oddlama/opkey/contplot.py

#!/usr/bin/env python3

import glob
import math
import numpy as np
import pandas as pd
import plotly
import plotly.graph_objects as go
import os
import sys
import scipy
import scipy.io.wavfile
from scipy import signal

triggerVelocityThreshold = 1.0
maxTriggerDelayUs = 40000
minTriggerJitterDelayUs = 15000
releasePositionThreshold = 0.4
releasePositionAbsolute = 0.15
pedalReleaseThreshold = 0.1
pedalPressThreshold = 0.2
velocityEmaAlpha = 0.1

def IsValidVelocityMaximum(pos, vel):
    return (vel >= 10.0) or ((pos > .25) and (vel > 3.0))

class LogicState:
    def __init__(self):
        self.lastUpdateTime = 0
        self.pos = 0.0
        self.vel = 0.0
        self.velEma = 0.0

        self.changed = False
        self.pressed = False

        self.lastPressTime = 0
        self.pressVelocity = 0.0
        self.lastReleaseTime = 0

        self.maxVelTime = 0
        self.maxVel = 0.0
        self.maxVelEma = 0.0
        self.maxVelPos = 0.0

    def nextState(self, now, deltaTime, newData):
        velEmaAlpha = 0.1

        prevPos = self.pos
        prevVel = self.vel
        self.pos = newData
        self.vel = (self.pos - prevPos) * (1000000.0 / deltaTime)
        self.velEma = self.velEma * (1.0 - velEmaAlpha) + self.vel * velEmaAlpha

        self.changed = False
        if self.pressed:
            if (self.pos < releasePositionAbsolute) or ((self.maxVelPos - self.pos) > releasePositionThreshold * self.maxVelPos):
                self.pressed = False
                self.changed = True
                self.lastReleaseTime = now

                self.maxVelTime = 0
                self.maxVel = 0.0
                self.maxVelEma = 0.0
                self.maxVelPos = 0.0
        else:
            if self.vel > self.maxVel:
                if IsValidVelocityMaximum(self.pos, self.vel):
                    self.maxVelTime = now
                    self.maxVel = self.vel
                    self.maxVelEma = self.velEma
                    self.maxVelPos = self.pos

            if (prevVel > triggerVelocityThreshold) and (self.vel <= triggerVelocityThreshold):
                if ((now - self.maxVelTime) <= maxTriggerDelayUs) and (now - self.lastReleaseTime > minTriggerJitterDelayUs):
                    self.pressed = True
                    self.changed = True
                    self.lastPressTime = self.maxVelTime

                    linearMaxVelocity = 50.0
                    linearRange = 0.75
                    compressedMaxVelocity = 110.0

                    self.pressVelocity = self.maxVel - self.maxVelEma
                    if self.pressVelocity < 0.0:
                        self.pressVelocity = 0.0
                    elif self.pressVelocity < linearMaxVelocity:
                        self.pressVelocity = linearRange * self.pressVelocity / linearMaxVelocity
                    elif self.pressVelocity < compressedMaxVelocity:
                        self.pressVelocity = linearRange + (1.0 - linearRange) * (self.pressVelocity - linearMaxVelocity) / (compressedMaxVelocity - linearMaxVelocity)
                    else:
                        self.pressVelocity = 1.0
                else:
                    self.maxVelTime = 0
                    self.maxVel = 0.0
                    self.maxVelEma = 0.0
                    self.maxVelPos = 0.0

# Config
includeRaw=True

# Constants (DONT CHANGE!)
plotAxisPos = "y"
plotAxisPosRaw = "y3"
plotAxisVel = "y2"
plotAxisVelRaw = "y4"
plotAxisWav = "y5"
plotAxisTriggers = plotAxisPosRaw

maxKeyFreqDeviation = 0.05
keyFrequencies = {
    'A0'    : 27.50000, 'A+0'   : 29.13524, 'B0'    : 30.86771, 'C1'    : 32.70320,
    'C+1'   : 34.64783, 'D1'    : 36.70810, 'D+1'   : 38.89087, 'E1'    : 41.20344,
    'F1'    : 43.65353, 'F+1'   : 46.24930, 'G1'    : 48.99943, 'G+1'   : 51.91309,
    'A1'    : 55.00000, 'A+1'   : 58.27047, 'B1'    : 61.73541, 'C2'    : 65.40639,
    'C+2'   : 69.29566, 'D2'    : 73.41619, 'D+2'   : 77.78175, 'E2'    : 82.40689,
    'F2'    : 87.30706, 'F+2'   : 92.49861, 'G2'    : 97.99886, 'G+2'   : 103.8262,
    'A2'    : 110.0000, 'A+2'   : 116.5409, 'B2'    : 123.4708, 'C3'    : 130.8128,
    'C+3'   : 138.5913, 'D3'    : 146.8324, 'D+3'   : 155.5635, 'E3'    : 164.8138,
    'F3'    : 174.6141, 'F+3'   : 184.9972, 'G3'    : 195.9977, 'G+3'   : 207.6523,
    'A3'    : 220.0000, 'A+3'   : 233.0819, 'B3'    : 246.9417, 'C4'    : 261.6256,
    'C+4'   : 277.1826, 'D4'    : 293.6648, 'D+4'   : 311.1270, 'E4'    : 329.6276,
    'F4'    : 349.2282, 'F+4'   : 369.9944, 'G4'    : 391.9954, 'G+4'   : 415.3047,
    'A4'    : 440.0000, 'A+4'   : 466.1638, 'B4'    : 493.8833, 'C5'    : 523.2511,
    'C+5'   : 554.3653, 'D5'    : 587.3295, 'D+5'   : 622.2540, 'E5'    : 659.2551,
    'F5'    : 698.4565, 'F+5'   : 739.9888, 'G5'    : 783.9909, 'G+5'   : 830.6094,
    'A5'    : 880.0000, 'A+5'   : 932.3275, 'B5'    : 987.7666, 'C6'    : 1046.502,
    'C+6'   : 1108.731, 'D6'    : 1174.659, 'D+6'   : 1244.508, 'E6'    : 1318.510,
    'F6'    : 1396.913, 'F+6'   : 1479.978, 'G6'    : 1567.982, 'G+6'   : 1661.219,
    'A6'    : 1760.000, 'A+6'   : 1864.655, 'B6'    : 1975.533, 'C7'    : 2093.005,
    'C+7'   : 2217.461, 'D7'    : 2349.318, 'D+7'   : 2489.016, 'E7'    : 2637.020,
    'F7'    : 2793.826, 'F+7'   : 2959.955, 'G7'    : 3135.963, 'G+7'   : 3322.438,
    'A7'    : 3520.000, 'A+7'   : 3729.310, 'B7'    : 3951.066, 'C8'    : 4186.009,
    'Soft'  : 0.0,
    'Damp'  : 0.0,
}

def butter_bandpass(lowcut, highcut, fs, order=5):
    nyq = 0.5 * fs
    low = lowcut / nyq
    high = highcut / nyq
    b, a = signal.butter(order, [low, high], btype='band')
    return b, a

def butter_bandpass_filter(data, lowcut, highcut, fs, order=5):
    b, a = butter_bandpass(lowcut, highcut, fs, order=order)
    y = signal.lfilter(b, a, data)
    return y

def running_mean(x, N):
    cumsum = np.cumsum(np.insert(x, 0, 0))
    return (cumsum[N:] - cumsum[:-N]) / float(N)


#def butter_lowpass(cutoff, fs, order):
#    nyq = 0.5 * fs
#    normal_cutoff = cutoff / nyq
#    b, a = signal.butter(order, normal_cutoff, btype='low', analog=False)
#    return b, a
#
#def butter_lowpass_filter(data, cutoff, fs, order=5):
#    b, a = butter_lowpass(cutoff, fs, order=order)
#    y = signal.lfilter(b, a, data)
#    return y
#
#cutoff=50
#fs=1000000/(csv['time'].iloc[-1]/len(csv['time']))

def getInputFiles(inputPath):
    if os.path.isdir(inputPath):
        path = inputPath
        fileBasenames = glob.glob(os.path.join(path, "*.raw"))
        fileBasenames = [os.path.basename(f) for f in fileBasenames if os.path.isfile(f)]
        fileBasenames.sort(key=lambda f: os.path.getmtime(os.path.join(path, f)))
    elif os.path.isfile(inputPath):
        path = os.path.dirname(inputPath)
        fileBasenames = [os.path.basename(inputPath)]
    else:
        print("error: Given path is neither a directory nor a .raw file'".format(path))
        sys.exit(1)

    return (path, fileBasenames)

def setFigureLayout(fig):
    fig.update_traces(mode='lines')
    fig.update_layout(
        xaxis=dict(
            title="Time (ms)",
            domain=[.04,.92] if includeRaw else [0.0, 1.0],
            ),
        yaxis=dict(
            title="Position",
            overlaying="y",
            anchor="x",
            side="left",
            ),
        yaxis2=dict(
            title="Velocity",
            overlaying="y",
            anchor="x",
            side="right",
            ),
        yaxis5=dict(
            title="dB",
            overlaying="y",
            anchor="free",
            side="right",
            position=1.0,
            ),
        )
    if includeRaw:
        fig.update_layout(
            yaxis3=dict(
                title="Raw Position",
                overlaying="y",
                anchor="free",
                side="left",
                position=0.0,
                ),
            yaxis4=dict(
                title="Raw Velocity",
                overlaying="y",
                anchor="free",
                side="right",
                position=0.96,
                ),
            )
    fig.update_layout(
        template='plotly_dark',
        title="Sensor Plot"
        )

class Meta:
    def __init__(self, file):
        try:
            with open(file, 'r') as f:
                content = f.readlines()
            content = [l.strip() for l in content]
        except IOError:
            raise IOError("Could not open meta file '{}'".format(file))

        if len(content) != 5:
            raise IOError("Invalid meta content length")

        self.uniqueSessionId = int(content[0])
        self.hostOverallBegin = int(content[1])
        self.hostBegin = int(content[2])
        self.hostEnd = int(content[3])
        self.mcuElapsed = int(content[4])

    def getUniqueSessionId(self):
        return self.uniqueSessionId

    def getOverallBeginUsHost(self):
        return self.hostOverallBegin

    def getBeginUsHost(self):
        return self.hostBegin

    def getEndUsHost(self):
        return self.hostEnd

    def getElapsedUsHost(self):
        return self.hostEnd - self.hostBegin

    def getElapsedUsMcu(self):
        return self.mcuElapsed

    def getOverallOffsetSec(self):
        return (self.hostBegin - self.hostOverallBegin) / 1000000

class Capture:
    def __init__(self):
        pass

    @classmethod
    def fromFile(cls, path, basename):
        c = cls()
        c.path = path
        c.basename = basename
        c.name = os.path.splitext(basename)[0]
        c.meta = Meta(c.__getMetaFile())

        tokens = c.name.split('_')
        c.sensorName = tokens[1]
        c.num = tokens[2]
        c.identifier = "{}, #{}".format(c.sensorName, c.num)

        c.__readData()
        return c

    @classmethod
    def fromCaptures(cls, captures):
        c = cls()
        c.path = captures[0].path
        c.basename = captures[0].basename
        c.name = captures[0].name
        #c.meta = Meta(c.__getMetaFile())

        c.sensorName = captures[0].sensorName
        c.num = captures[-1].num
        c.identifier = "{}".format(c.sensorName)

        c.count = 0
        c.t = []
        c.tTriggers = []
        c.yTriggers = []
        c.rawPos = []
        c.rawVel = []
        c.wavT = []
        c.wavY = []
        for capture in captures:
            c.count += capture.count
            c.t.extend(capture.t)
            c.tTriggers.extend(capture.tTriggers)
            c.yTriggers.extend(capture.yTriggers)
            c.rawPos.extend(capture.rawPos)
            c.rawVel.extend(capture.rawVel)
            c.wavT.extend(capture.wavT)
            c.wavY.extend(capture.wavY)
        return c

    def __getRawFile(self):
        return os.path.join(self.path, self.basename)

    def __getMetaFile(self):
        return "{}.meta".format(self.__getRawFile())

    def getPlotHtmlFile(self):
        return "{}.html".format(os.path.join(self.path, self.name))

    def getWavFile(self):
        return os.path.join(self.path, "{}.wav".format(self.meta.uniqueSessionId))

    def getIdentifier(self):
        return self.identifier

    def __readData(self):
        # Read data
        self.csv = pd.read_csv(self.__getRawFile(), names=['time', 'dt', 'value'])

        self.rawTime = self.csv['time'].values
        self.rawDt = self.csv['dt'].values
        self.rawSensorData = self.csv['value'].values

        self.tTriggers = []
        self.yTriggers = []
        logicState = LogicState()
        for i in range(len(self.rawDt)):
            logicState.nextState(self.rawTime[i], self.rawDt[i], self.rawSensorData[i])
            if logicState.changed:
                if logicState.pressed:
                    self.tTriggers += [self.rawTime[i]]
                    self.yTriggers += [1]
                else:
                    self.tTriggers += [self.rawTime[i]]
                    self.yTriggers += [0]

        # General information
        self.count = len(self.rawSensorData)
        #self.tStep = (self.meta.getElapsedNsMcu() / 1000000000) / self.count
        #if self.tStep < 4000:
        #    frac = int(0.004 / self.tStep)
        #    self.tStep *= frac
        #    self.rawSensorData = [self.rawSensorData[i] for i in range(0, self.count, frac)]
        #    self.count = len(self.rawSensorData)

        #self.tStepInv = self.count / (self.meta.getElapsedNsMcu() / 1000000000)

        #self.t0 = self.rawTime[0]
        #self.t = [(x - self.t0) / 1000 for x in self.csv['time'].values]
        self.t = [self.meta.getOverallOffsetSec() + i / 1000000 for i in self.rawTime]
        self.rawPos = self.rawSensorData
        self.rawVel = [0] + [(self.rawPos[i + 1] - self.rawPos[i]) * (1000000.0 / self.rawDt[i + 1]) for i in range(len(self.rawPos) - 1)]

        ### Calculate pos and vel
        ##self.rawPos = self.rawSensorData
        ##self.rawVel = np.insert(np.diff(self.rawPos) * self.tStepInv, 0, 0)
        ##global aat
        ##aat = .0
        ##def accumTen(i):
        ##    global aat
        ##    aat = aat * .9 + i * .1
        ##    return aat
        ##self.emaPos = [accumTen(i) for i in self.rawPos]
        ##global bbt
        ##bbt = .0
        ##def accumTen2(i):
        ##    global bbt
        ##    if i < bbt:
        ##        bbt = bbt * .7 + i * .3
        ##    else:
        ##        bbt = bbt * .9 + i * .1
        ##    return bbt
        ##self.emaVel = [accumTen2(i) for i in self.rawVel]
        ###self.smoothPos = signal.savgol_filter(self.rawPos, 153, 3)
        ###self.smoothVel = signal.savgol_filter(self.rawVel, 153, 3)

        ### Calculate time shift
        ##self.indexT0 = np.where(self.rawVel == np.amax(self.rawVel))[0][0]
        ##self.t0 = -self.csv['time'].values[self.indexT0]
        ##self.t = [(self.t0 + x) / 1000 for x in self.csv['time'].values]

        ### Calculate t0 based velocity
        ##self.t0Vel = [(e - self.rawPos[self.indexT0]) * 1000000 / (self.t[i] - self.t0) for i,e in enumerate(self.rawPos)]

        wavFile = self.getWavFile()
        (self.audioFs, self.audioData) = scipy.io.wavfile.read(wavFile)
        if self.audioData.shape[1] == 2:
            self.audioData = self.audioData[:,0]
        if self.audioData.dtype == np.int16:
            self.audioData = self.audioData / (2**(16-1))
        elif self.audioData.dtype == np.int32:
            self.audioData = self.audioData / (2**(32-1))

        lowcut = keyFrequencies[self.sensorName] * (1.0 - maxKeyFreqDeviation)
        highcut = keyFrequencies[self.sensorName] * (1.0 + maxKeyFreqDeviation)
        #print("lowcut {}, highcut {}".format(lowcut, highcut))

        #self.audioData = butter_bandpass_filter(self.audioData, lowcut, highcut, self.audioFs)

        recordOffset = 0.953
        #displayRange = (self.t[0], ccap.t[-1])
        #readRange = (recordOffset, recordOffset + (displayRange[1] - displayRange[0]))

        #first = int(readRange[0] * self.audioFs)
        #last = int(readRange[1] * self.audioFs)

        #self.wavT = np.linspace(displayRange[0], displayRange[1], num=(last - first))

        self.wavY = np.array(self.audioData)
        self.audioDuration = len(self.wavY) / self.audioFs
        self.wavOffset = self.meta.getOverallOffsetSec() - recordOffset
        self.wavT = np.linspace(self.wavOffset, self.wavOffset + self.audioDuration, num=len(self.wavY))

        maskedWavY = np.ma.masked_where(np.abs(self.wavY) < .001, self.wavY)
        maskedWavT = np.ma.masked_where(np.ma.getmask(maskedWavY), self.wavT)
        self.wavY = maskedWavY.compressed()
        self.wavT = maskedWavT.compressed()

        ## get the maximum for buckets of 5 ms each
        #bucketEach = 0.005
        #buckets = int(len(self.wavY) / (bucketEach * self.audioFs))
        #split = np.array_split(self.wavY, buckets)
        #self.wavY = []
        #for i in split:
        #    self.wavY += [np.amax(i)]

        #self.wavY = np.amax(np.stack(split, axis=0), axis=1)
        #self.wavT = np.linspace(displayRange[0], displayRange[1], num=len(self.wavY))
        #self.wavY = 20 * np.log10(self.wavY)

        #wavD = np.diff(np.append(self.wavY, 0))
        #maskedWavY = np.ma.masked_where(np.abs(wavD) < .02, np.abs(self.wavY))
        #maskedWavT = np.ma.masked_where(np.ma.getmask(maskedWavY), self.wavT)
        #self.wavY = maskedWavY.compressed()
        #self.wavT = maskedWavT.compressed()

        print("wav percentage: {}".format(100 * len(self.wavT) / (self.audioDuration * self.audioFs)))

    def plotPos(self, fig):
        print("plotting position...")
        #fig.add_trace(go.Scattergl(
        #    name='{} pos'.format(self.getIdentifier()),
        #    x=self.t,
        #    y=self.smoothPos,
        #    yaxis=plotAxisPos,
        #))
        if includeRaw:
            fig.add_trace(go.Scattergl(
                name='{} raw pos'.format(self.getIdentifier()),
                x=self.t,
                y=self.rawPos,
                yaxis=plotAxisPosRaw,
            ))

    def plotVel(self, fig):
        print("plotting velocity...")
        #fig.add_trace(go.Scattergl(
        #    name='{} vel'.format(self.getIdentifier()),
        #    x=self.t,
        #    y=self.smoothVel,
        #    yaxis=plotAxisVel,
        #))
        #fig.add_trace(go.Scattergl(
        #    name='{} t0 vel'.format(self.getIdentifier()),
        #    x=self.t,
        #    y=self.t0Vel,
        #    yaxis=plotAxisVel,
        #))
        if includeRaw:
            #global aat
            #aat = .0
            #def accumTen(i):
            #    global aat
            #    aat = aat * .9 + i * .1
            #    #aat = aat * .999 + i * .001
            #    return aat
            #tendency = [accumTen(i) for i in self.rawPos]
            fig.add_trace(go.Scattergl(
                name='{} raw vel'.format(self.getIdentifier()),
                x=self.t,
                y=self.rawVel,
                yaxis=plotAxisVelRaw,
            ))
            #fig.add_trace(go.Scattergl(
            #    name='{} pos ema'.format(self.getIdentifier()),
            #    x=self.t,
            #    y=self.emaPos,
            #    yaxis=plotAxisPosRaw,
            #))
            #fig.add_trace(go.Scattergl(
            #    name='{} vel ema'.format(self.getIdentifier()),
            #    x=self.t,
            #    y=self.emaVel,
            #    yaxis=plotAxisVelRaw,
            #))

    def plotAudio(self, fig):
        print("plotting audio...")
        fig.add_trace(go.Scattergl(
            name='{} wav'.format(ccap.getIdentifier()),
            x=self.wavT,
            y=self.wavY,
            yaxis=plotAxisWav,
        ))

    def plotTriggers(self, fig):
        print("plotting triggers...")
        fig.add_trace(go.Scattergl(
            name='{} wav'.format(ccap.getIdentifier()),
            x=self.tTriggers,
            y=self.yTriggers,
            yaxis=plotAxisTriggers,
        ))
    #    if self.audioData is None:
    #        return

    #    recordOffset = 1.0 - 0.06

    #    t0 = self.t0 / 1000000
    #    mcuSampleLength = (self.meta.getElapsedNsMcu() / 1000000000)

    #    readRange = (recordOffset, recordOffset + mcuSampleLength)
    #    displayRange = (t0, t0 + mcuSampleLength)

    #    first = int(readRange[0] * self.audioFs)
    #    last = int(readRange[1] * self.audioFs)
    #    tWav = np.linspace(displayRange[0] * 1000, displayRange[1] * 1000, num=(last - first))

    #    lowcut = keyFrequencies[self.sensorName] * (1.0 - maxKeyFreqDeviation)
    #    highcut = keyFrequencies[self.sensorName] * (1.0 + maxKeyFreqDeviation)

    #    fig.add_trace(go.Scattergl(
    #        name='{} wav (l)'.format(self.getIdentifier()),
    #        x=tWav,
    #        y=butter_bandpass_filter(self.audioData[first:last,0], lowcut, highcut, self.audioFs),
    #        yaxis=plotAxisWav,
    #    ))

    #    fig.add_trace(go.Scattergl(
    #        name='{} wav (r)'.format(self.getIdentifier()),
    #        x=tWav,
    #        y=butter_bandpass_filter(self.audioData[first:last,1], lowcut, highcut, self.audioFs),
    #        yaxis=plotAxisWav,
    #    ))

    def plot(self, fig):
        self.plotPos(fig)
        self.plotVel(fig)
        self.plotAudio(fig)
        self.plotTriggers(fig)

if __name__ == "__main__":
    if len(sys.argv) != 2:
        print("usage: plot.py <directory|file.raw>")
        sys.exit(1)

    (path, fileBasenames) = getInputFiles(sys.argv[1])

    captures = []
    for file in fileBasenames:
        try:
            print("reading {}".format(file))
            captures.append(Capture.fromFile(path, file))
        except IOError as e:
            print("Error while loading Capture:")
            print(e)
            continue

    print("combining...")
    ccap = Capture.fromCaptures(captures)
    fig = go.Figure()
    ccap.plot(fig)
    print("layouting...")
    setFigureLayout(fig)
    print("plotting...")
    plotly.offline.plot(fig, filename=ccap.getPlotHtmlFile(), auto_open=True)
    print("done")
