oddlama/opkey/main/nvs.cpp

#include "nvs.h"
#include "fmt.h"


namespace opkey::nvs {


void Init() {
	/* Initialize NVS (used to store opkey and bluetooth PHY calibration data) */
	if (nvs_flash_init() != ESP_OK) {
		esp::check(nvs_flash_erase(), "nvs_flash_erase()");
		esp::check(nvs_flash_init(), "nvs_flash_init()");
	}
}


} // namespace opkey::nvs
