oddlama/opkey/main/ble_service.h

#pragma once

#include "ble_meta.h"
#include "ble_uuid.h"
#include "ble_characteristic.h"


namespace opkey::ble {


struct ServiceMixinTag { };

namespace service_options {

struct Secondary : private ServiceMixinTag { };

} // namespace service_options


template<typename Tuple>
struct ExpandCharacteristicDefinitions;

template<typename... Ts>
struct ExpandCharacteristicDefinitions<std::tuple<Ts...>> {
	static inline constexpr const std::array<ble_gatt_chr_def, sizeof...(Ts) + 1> value =
		{ Ts::NimbleCharacteristicDefinition()...
		, { nullptr, nullptr, nullptr, nullptr, 0, 0, nullptr }
		};
};


struct ServiceTag { };

template<typename... Options>
struct Service : private ServiceTag {
	static_assert(meta::CountDerivedType<UuidTag, Options...> <= 1, "Service must not include more than one Uuid");
	static_assert(
			meta::CountDerivedType<ServiceMixinTag, Options...> +
			meta::CountDerivedType<UuidTag, Options...> +
			meta::CountDerivedType<CharacteristicTag, Options...> ==
				sizeof...(Options)
			, "Service definition contains an invalid type"
			);

	using Uuid = meta::GetDerivedType<UuidTag, UuidAuto, Options...>;
	using CharacteristicTuple = meta::ExtractDerivedTypes<CharacteristicTag, Options...>;
	static inline constexpr const auto nimbleGattCharacteristicDefinitions =
		ExpandCharacteristicDefinitions<CharacteristicTuple>::value;

	static inline constexpr const bool secondary = meta::HasType<service_options::Secondary, Options...>;

	constexpr static ble_gatt_svc_def NimbleServiceDefinition() noexcept {
		return
			{ // .type
				secondary ? BLE_GATT_SVC_TYPE_SECONDARY : BLE_GATT_SVC_TYPE_PRIMARY
			, // .uuid
				reinterpret_cast<const ble_uuid_t*>(&Uuid::nimbleUuid)
			, // .includes
				nullptr
			, // .characteristics
				nimbleGattCharacteristicDefinitions.data()
			};
	}
};


} // namespace opkey::ble
